Pertifiatus/MP3-Player/KiCad/Projekt 1/EASYEDA_MODELS/C0603_L1.6-W0.8-H0.8.step

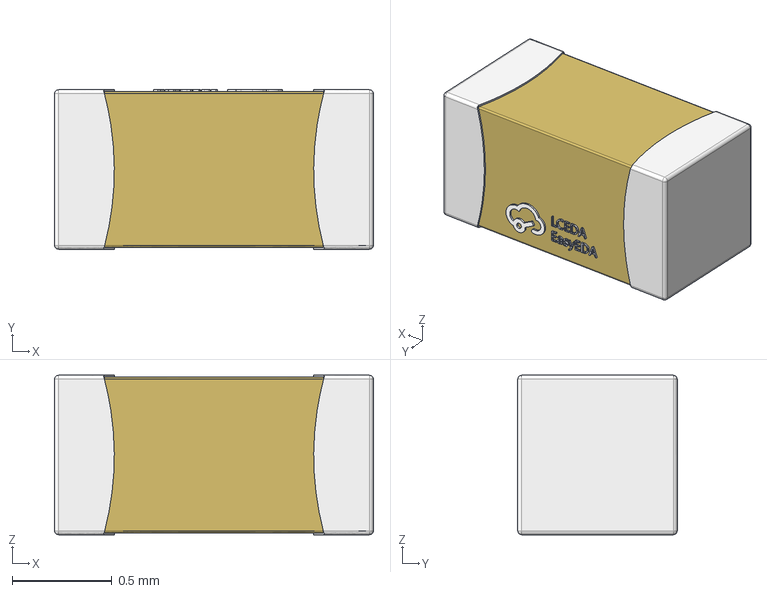
[picture p15: CAD file, 2026-08-18]
KiCad/Projekt 1/EASYEDA_MODELS/C0603_L1.6-W0.8-H0.8.step
1.60 x 0.8 x 0.8 mm
