Pertifiatus/MP3-Player/KiCad/Projekt 1/EASYEDA_MODELS/CONN-TH_PH2.00-LI-8P.step

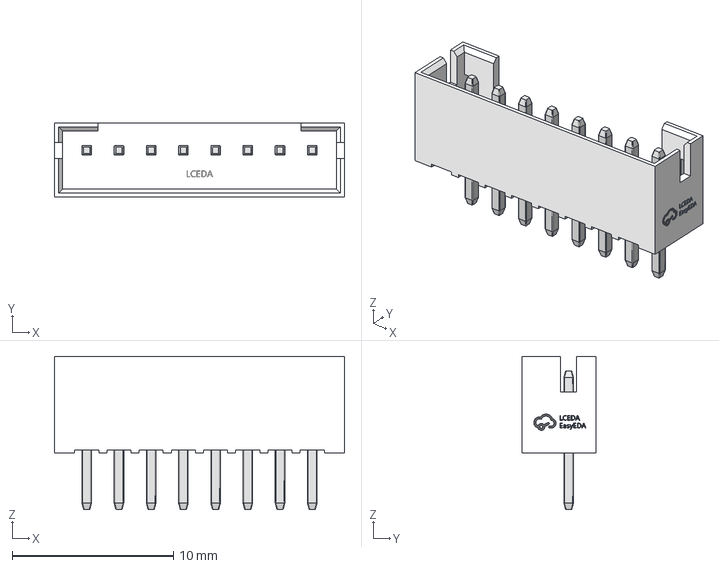
[picture p16: CAD file, 2026-08-18]
KiCad/Projekt 1/EASYEDA_MODELS/CONN-TH_PH2.00-LI-8P.step
18.0 x 4.60 x 9.50 mm
