Pertifiatus/MP3-Player/KiCad/Projekt 1/EASYEDA_MODELS/L2520.step

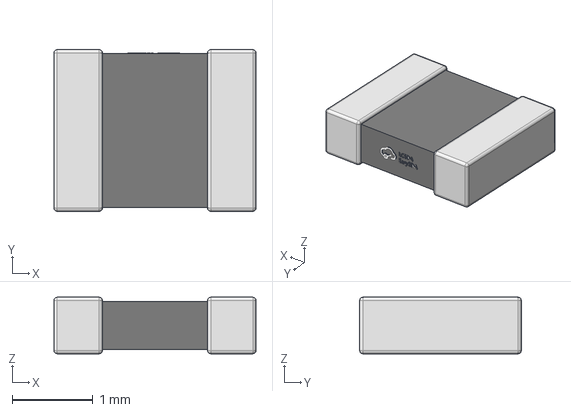
[picture p17: CAD file, 2026-08-18]
KiCad/Projekt 1/EASYEDA_MODELS/L2520.step
2.50 x 2.00 x 0.7 mm
