Pertifiatus/MP3-Player/KiCad/Projekt 1/EASYEDA_MODELS/CONN-TH_PH2.00-LI-2P.step

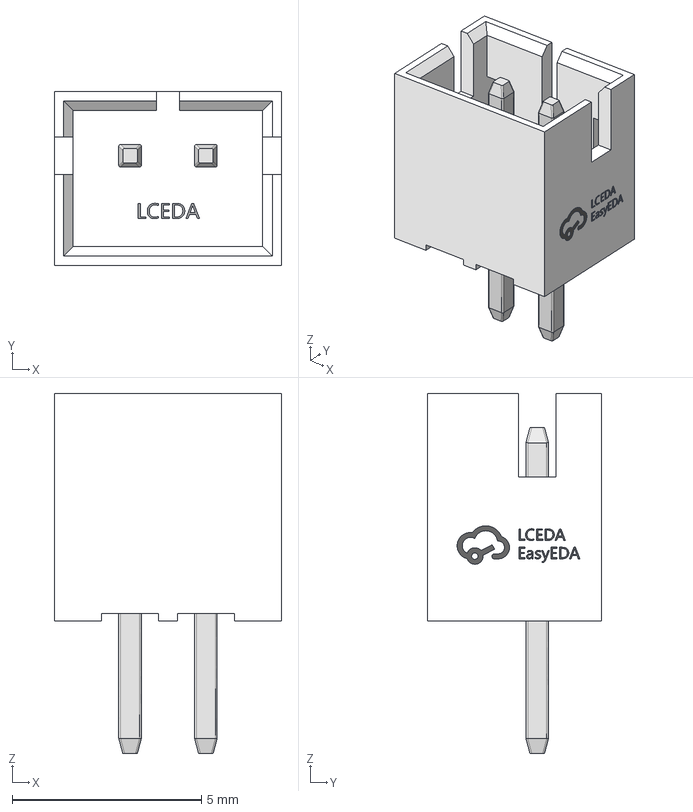
[picture p18: CAD file, 2026-08-18]
KiCad/Projekt 1/EASYEDA_MODELS/CONN-TH_PH2.00-LI-2P.step
6.00 x 4.60 x 9.50 mm
