Pertifiatus/MP3-Player/KiCad/Projekt 1/EASYEDA_MODELS/TDFN-8_L2.0-W2.0-P0.50-BL-EP1.2.step

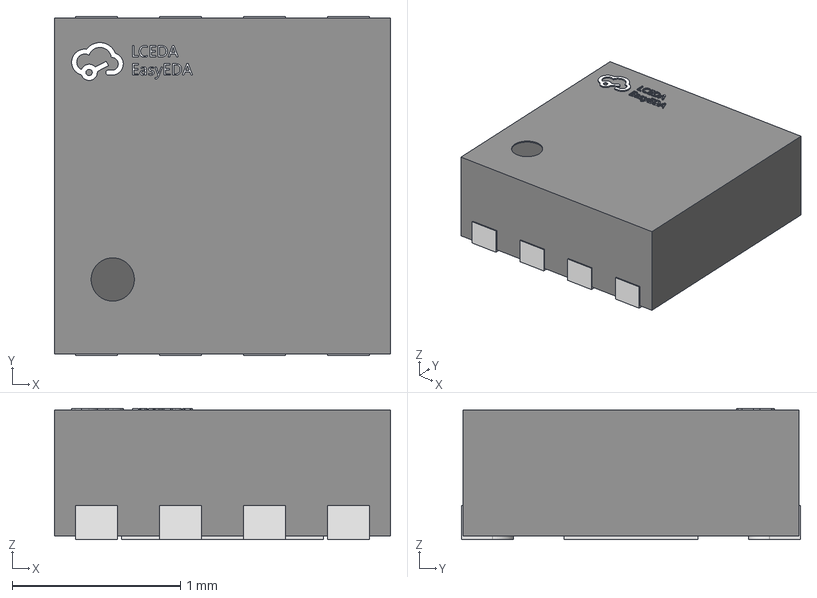
[picture p19: CAD file, 2026-08-18]
KiCad/Projekt 1/EASYEDA_MODELS/TDFN-8_L2.0-W2.0-P0.50-BL-EP1.2.step
2.00 x 2.02 x 0.78 mm
