Pertifiatus/MP3-Player/KiCad/Projekt 1/EASYEDA_MODELS/AUDIO-SMD_L11.8-W6.0-H5.0-4P.step

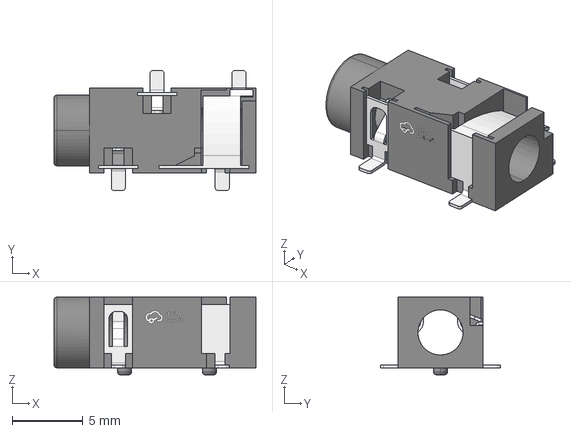
[picture p20: CAD file, 2026-08-18]
KiCad/Projekt 1/EASYEDA_MODELS/AUDIO-SMD_L11.8-W6.0-H5.0-4P.step
14.3 x 8.50 x 5.50 mm
