Pertifiatus/MP3-Player/Software/sdcard-boot-config.txt

# Vorlage für die Boot-Partition (G:\config.txt bzw. /boot/firmware/config.txt) einer
# frisch mit Raspberry Pi Imager geflashten Karte. Nach dem Flashen komplett so einfügen
# (ersetzt die von Imager generierte config.txt), bevor die Karte das erste Mal steckt.
# Siehe CLAUDE.md Abschnitt 3 ("config.txt — bekannt funktionierender Stand").

# For more options and information see
# http://rptl.io/configtxt
# Some settings may impact device functionality. See link above for details

# Uncomment some or all of these to enable the optional hardware interfaces
dtparam=i2c_arm=on
dtparam=i2s=on
dtparam=spi=on
dtoverlay=spi0-1cs,no_miso
dtoverlay=spi4-1cs

force_eeprom_read=0
disable_poe_fan=1

# Enable audio (loads snd_bcm2835)
dtparam=audio=on

# Additional overlays and parameters are documented
# /boot/firmware/overlays/README

# Automatically load overlays for detected cameras
camera_auto_detect=1

# Automatically load overlays for detected DSI displays
display_auto_detect=1

# Automatically load initramfs files, if found
auto_initramfs=1

# Enable DRM VC4 V3D driver
dtoverlay=vc4-kms-v3d
max_framebuffers=2

# Don't have the firmware create an initial video= setting in cmdline.txt.
# Use the kernel's default instead.
disable_fw_kms_setup=1

# Run in 64-bit mode
arm_64bit=1

# Disable compensation for displays with overscan
disable_overscan=1

# Run as fast as firmware / board allows
arm_boost=1

[cm4]
# Enable host mode on the 2711 built-in XHCI USB controller.
# This line should be removed if the legacy DWC2 controller is required
# (e.g. for USB device mode) or if USB support is not required.
otg_mode=1

[cm5]
dtoverlay=dwc2,dr_mode=host

[pi5]
dtoverlay=nospi10

[all]
